anaireorg/anaire-devices/Anaire.30ppm-50ppm/docs/Anaire50ppmBreadBox.jpg

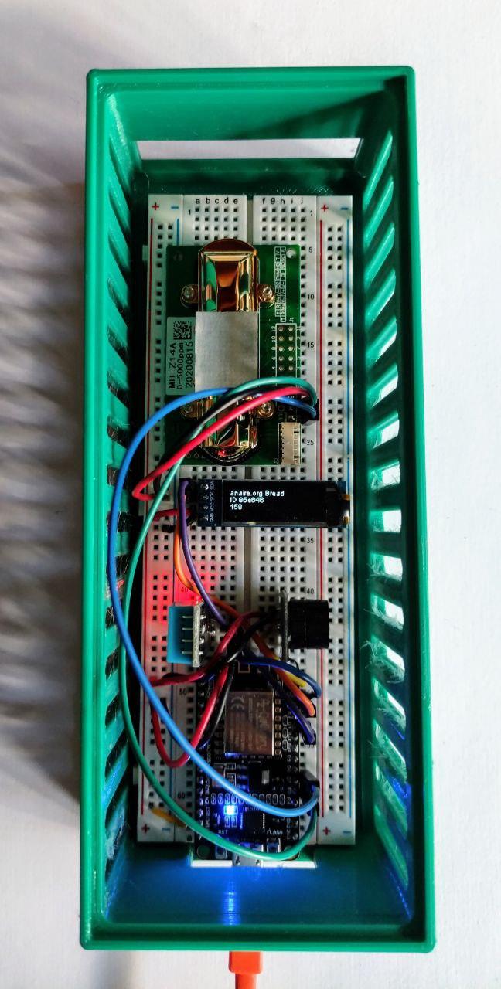
Anaire.30ppm-50ppm/docs/Anaire50ppmBreadBox.jpg
