anaireorg/anaire-devices/Anaire.PiCO2/docs/PiCO2 Frontal3.jpg

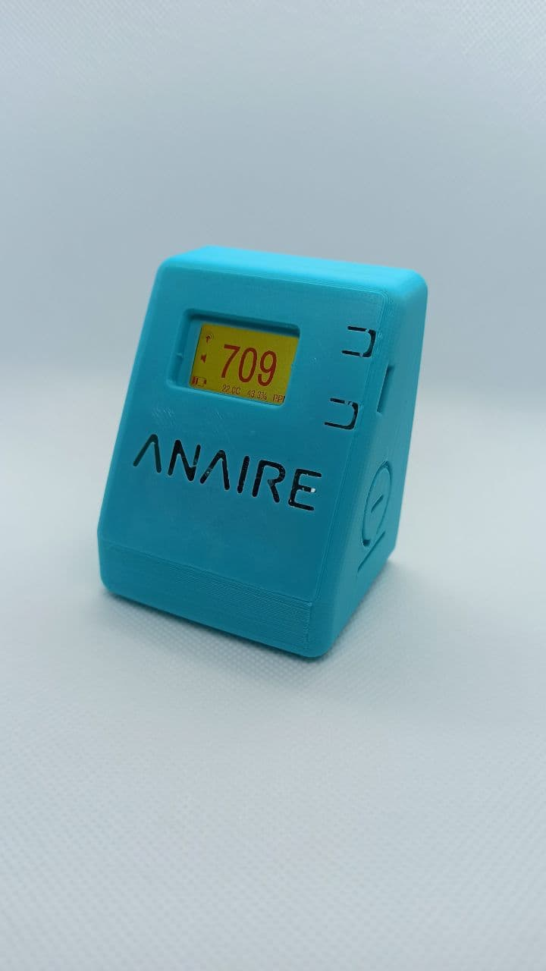
Anaire.PiCO2/docs/PiCO2 Frontal3.jpg
