anaireorg/anaire-devices/Anaire.PiCO2/docs/PiCO2 Frontal4.jpg

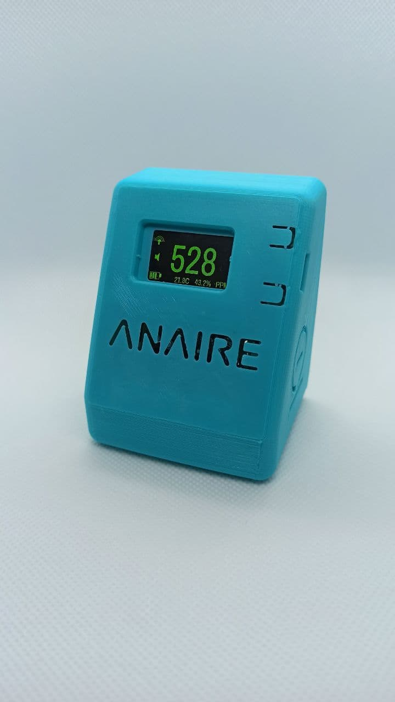
Anaire.PiCO2/docs/PiCO2 Frontal4.jpg
