anaireorg/anaire-devices/Anaire.PiCO2/docs/PiCO2 Frontal5.jpg

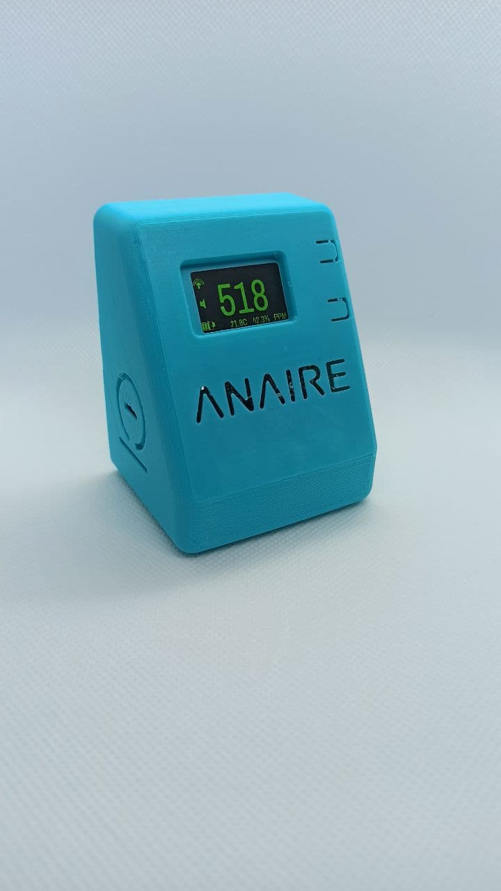
Anaire.PiCO2/docs/PiCO2 Frontal5.jpg
