anaireorg/anaire-devices/Anaire.PiCO2/docs/PiCO2 Frontal Alarma2.jpg

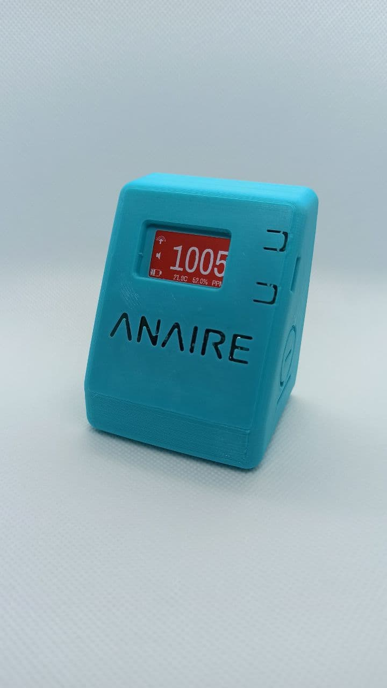
Anaire.PiCO2/docs/PiCO2 Frontal Alarma2.jpg
