anaireorg/anaire-devices/Anaire.PiCO2/docs/PiCO2 Frontal Alarma3.jpg

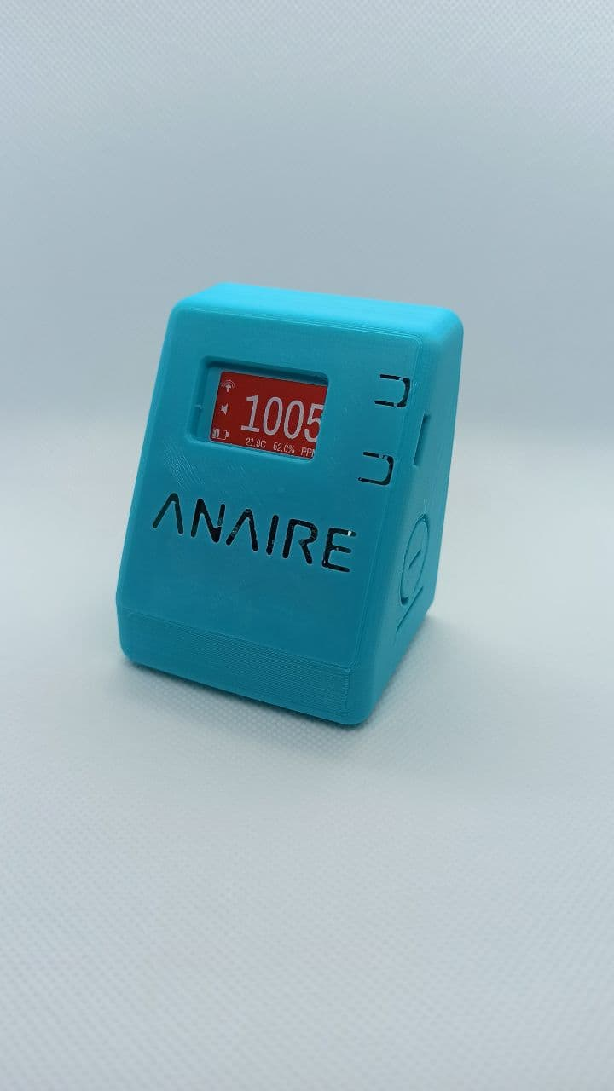
Anaire.PiCO2/docs/PiCO2 Frontal Alarma3.jpg
