anaireorg/anaire-devices/Anaire.PiCO2/docs/PiCO2 Frontal Monitor.jpg

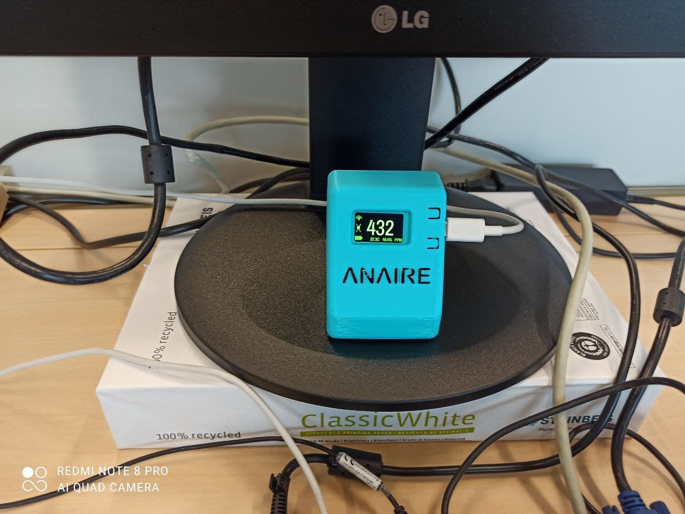
Anaire.PiCO2/docs/PiCO2 Frontal Monitor.jpg
