anaireorg/anaire-devices/Anaire.PiCO2/docs/PiCO2 Frontal.jpg

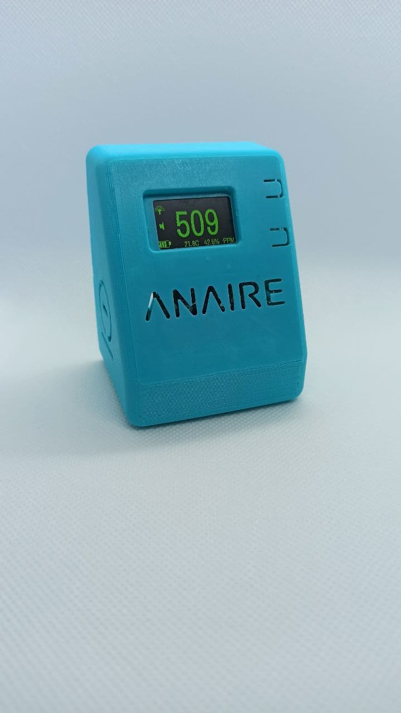
Anaire.PiCO2/docs/PiCO2 Frontal.jpg
